wil92/keyboard-pcb/common/usb-245.step

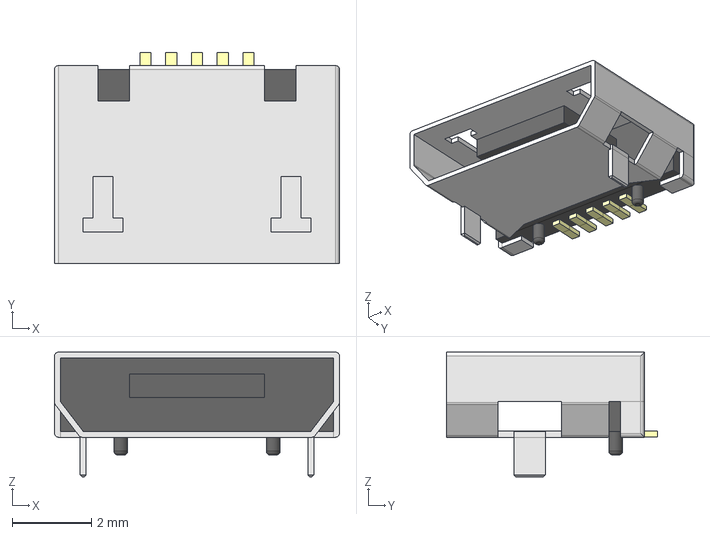
[picture p17: CAD file, 2023-01-02]
common/usb-245.step
7.20 x 5.33 x 3.15 mm
