wil92/keyboard-pcb/common/SW_Cherry_MX_PCB.stp

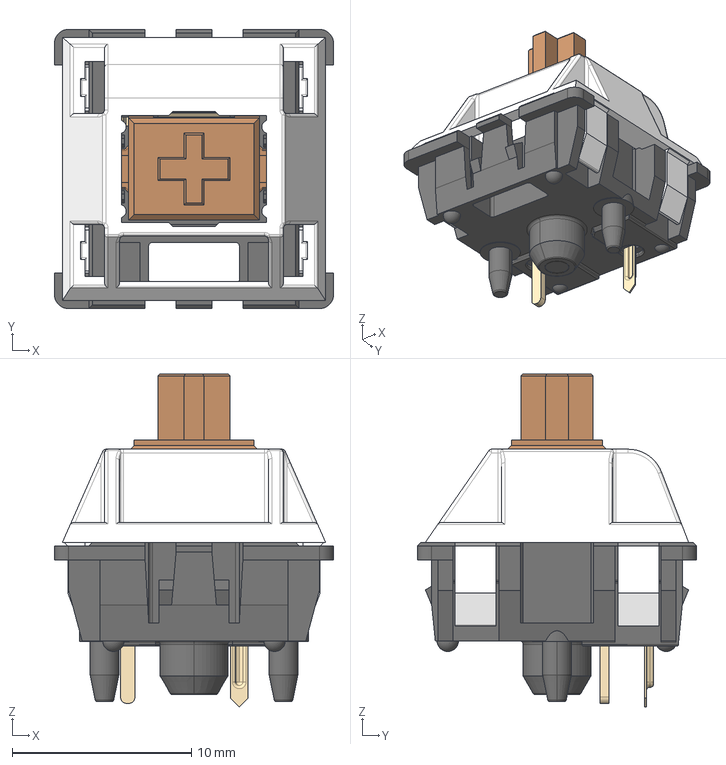
[picture p18: CAD file, 2022-07-31]
common/SW_Cherry_MX_PCB.stp
15.6 x 15.6 x 18.6 mm
