wil92/keyboard-pcb/keyboard-personal/keyboard-box/slice-keyboard.stl

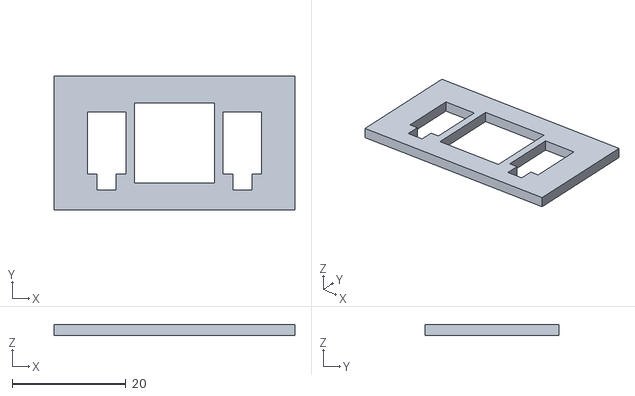
[picture p19: CAD file, 2024-05-21]
keyboard-personal/keyboard-box/slice-keyboard.stl
42.4 x 23.6 x 2.00
